xdesig/Plac_soldadura/Plataforma_sold_ATmega328p/Imaxes/IMG_20260528_120613.jpg

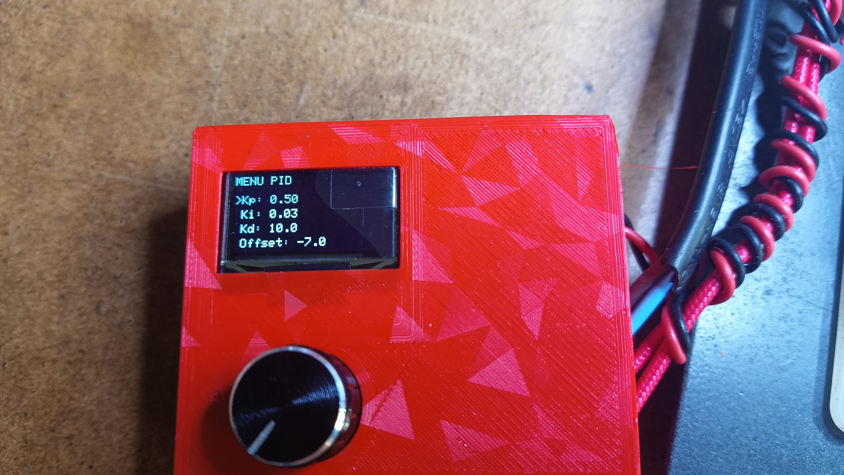
Plataforma_sold_ATmega328p/Imaxes/IMG_20260528_120613.jpg
