xdesig/Plac_soldadura/Plataforma_sold_ATmega328p/Imaxes/IMG_20260720_120905.jpg

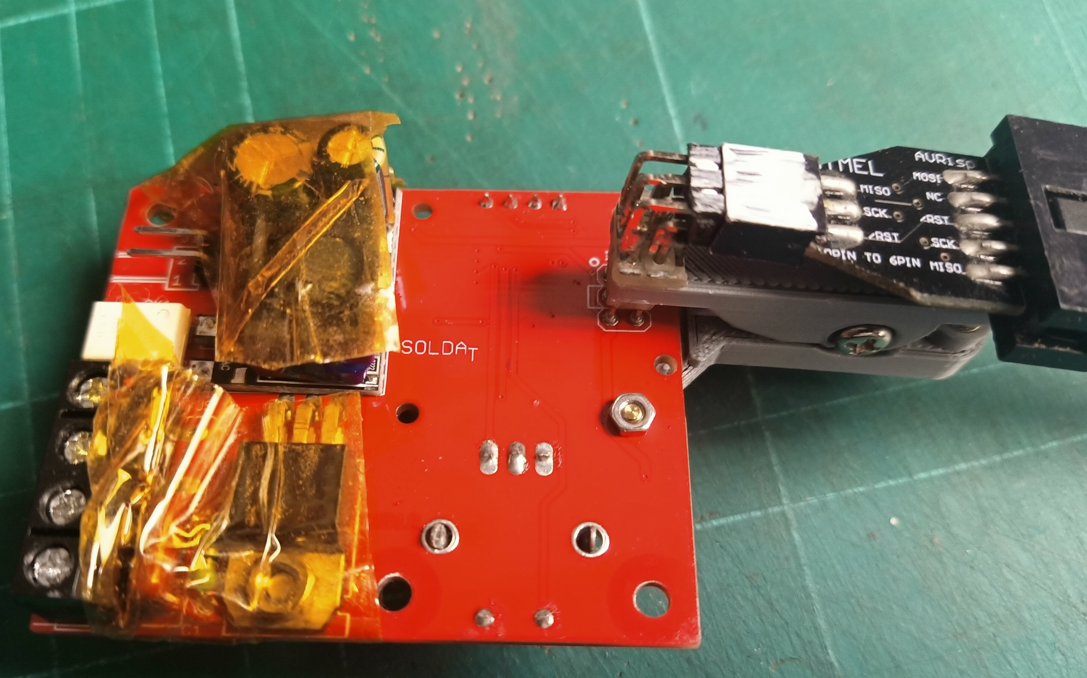
Plataforma_sold_ATmega328p/Imaxes/IMG_20260720_120905.jpg
