xdesig/Plac_soldadura/Plataforma_sold_ATmega328p/Imaxes/IMG_20260720_120916.jpg

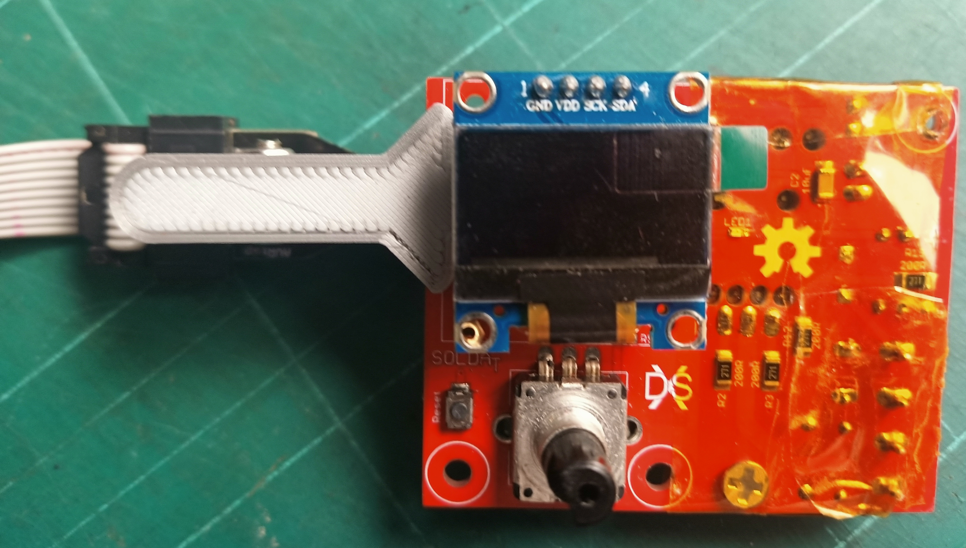
Plataforma_sold_ATmega328p/Imaxes/IMG_20260720_120916.jpg
