xdesig/Plac_soldadura/Plataforma_sold_ESP32-C3/Caixa/Plataforma_soldadora_3-4.png

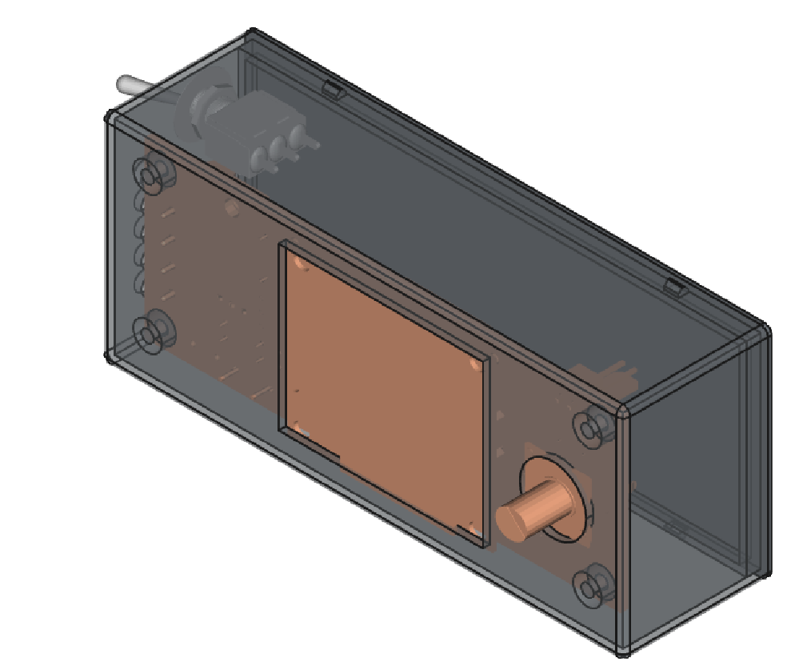
Plataforma_sold_ESP32-C3/Caixa/Plataforma_soldadora_3-4.png
