xdesig/Plac_soldadura/Plataforma_sold_ESP32-C3/Imaxes/ac-dc_5V700mA.png

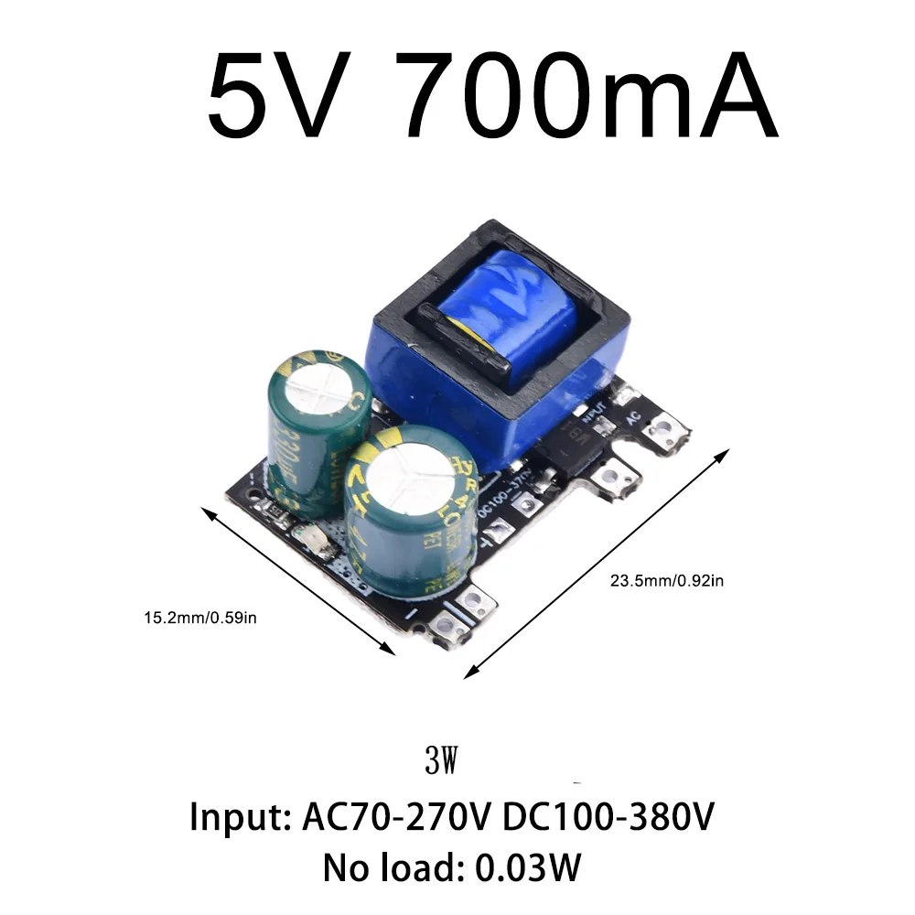
Plataforma_sold_ESP32-C3/Imaxes/ac-dc_5V700mA.png
