xdesig/Plac_soldadura/Plataforma_sold_ESP32-C3/Imaxes/eagleUp_Plataforma_soldadora_board_top.png

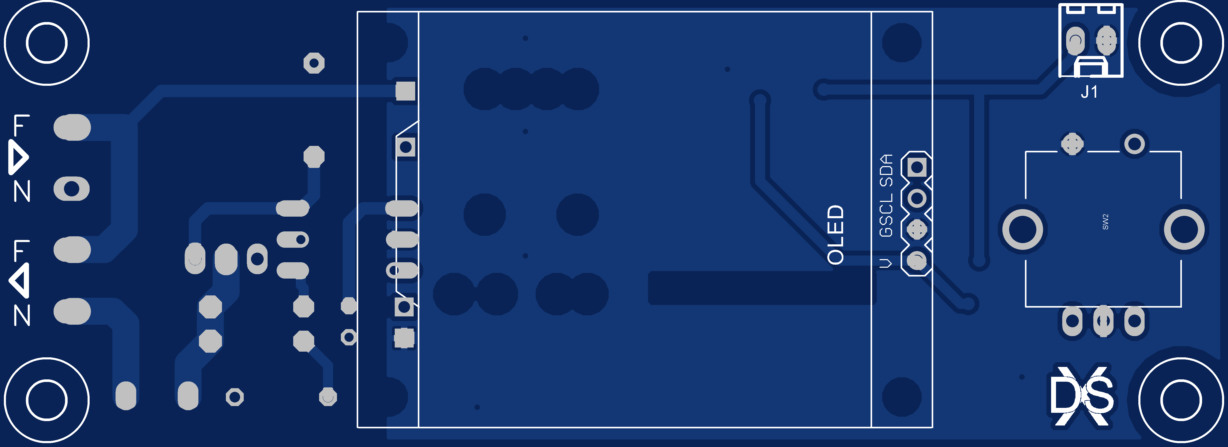
Plataforma_sold_ESP32-C3/Imaxes/eagleUp_Plataforma_soldadora_board_top.png
