xdesig/Plac_soldadura/Plataforma_sold_ESP32-C3/Imaxes/ESP32-C3.webp

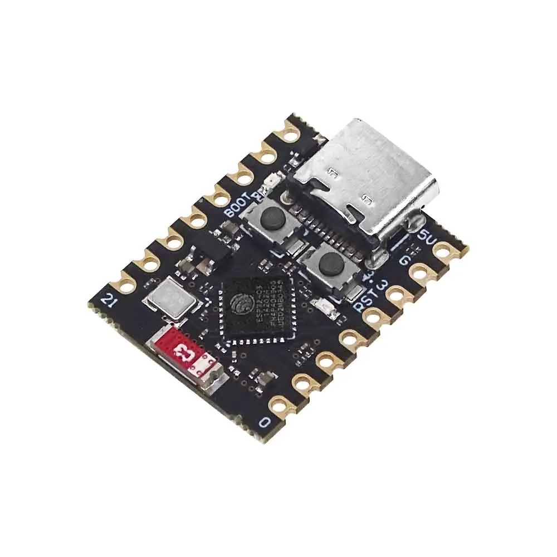
Plataforma_sold_ESP32-C3/Imaxes/ESP32-C3.webp
