xdesig/Plac_soldadura/Plataforma_sold_ESP32-C3/Imaxes/Plataforma_soldadora_2.png

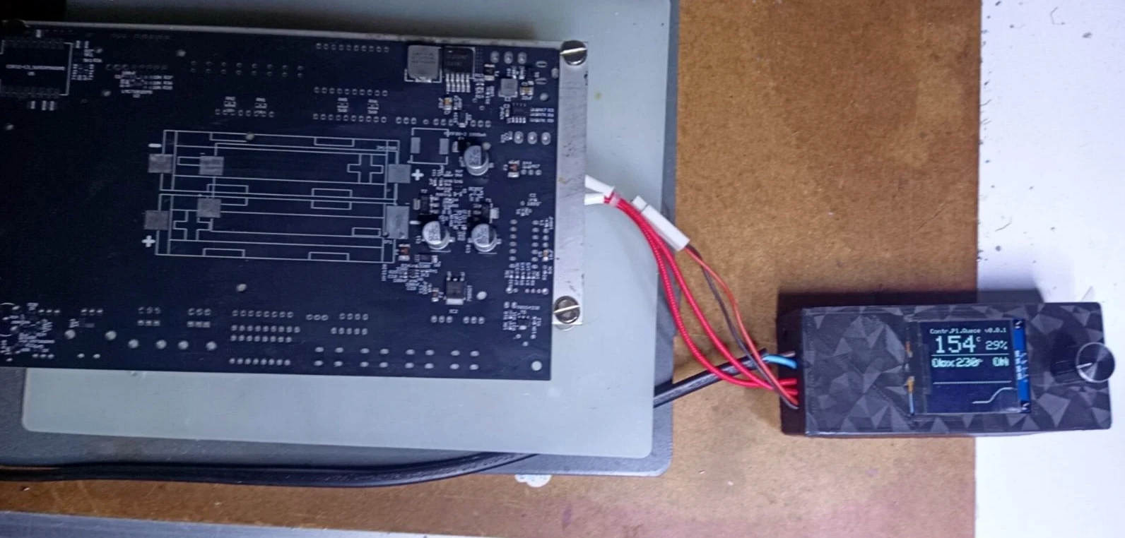
Plataforma_sold_ESP32-C3/Imaxes/Plataforma_soldadora_2.png
