xdesig/Plac_soldadura/Plataforma_sold_ESP32-C3/Imaxes/Rotary_encoder.webp

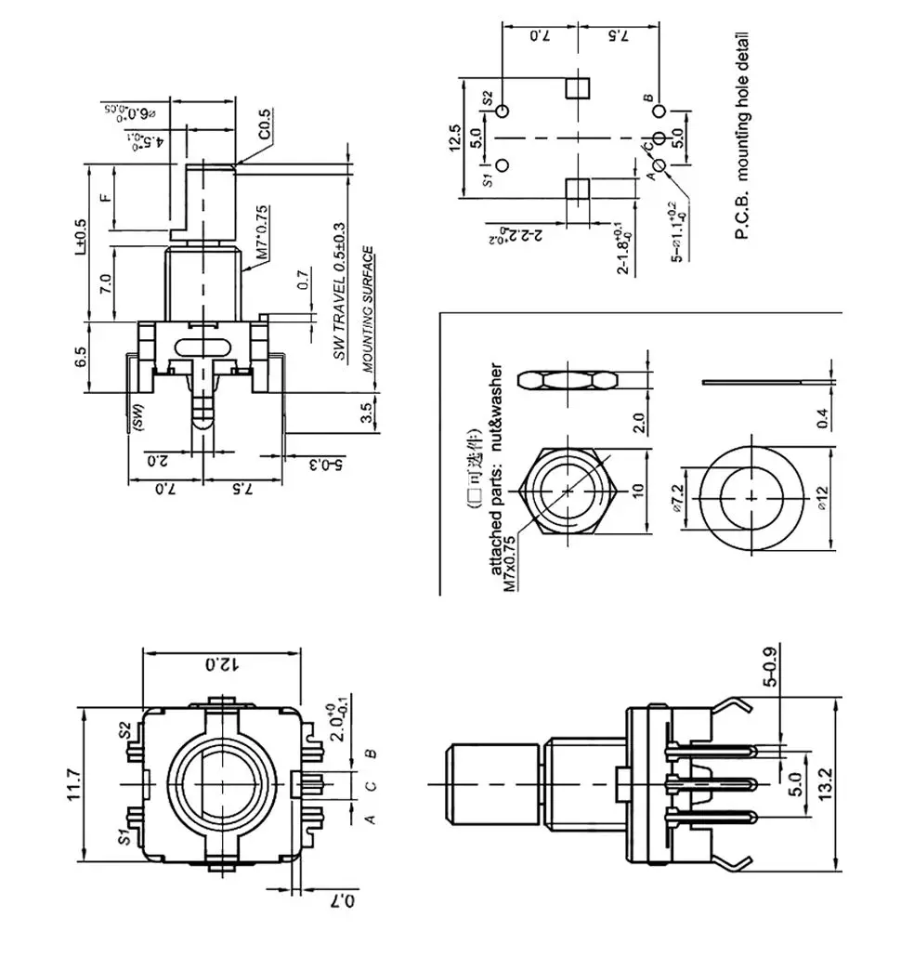
Plataforma_sold_ESP32-C3/Imaxes/Rotary_encoder.webp
